kyudomaster/chu_giga/CAD/chu-tof.step

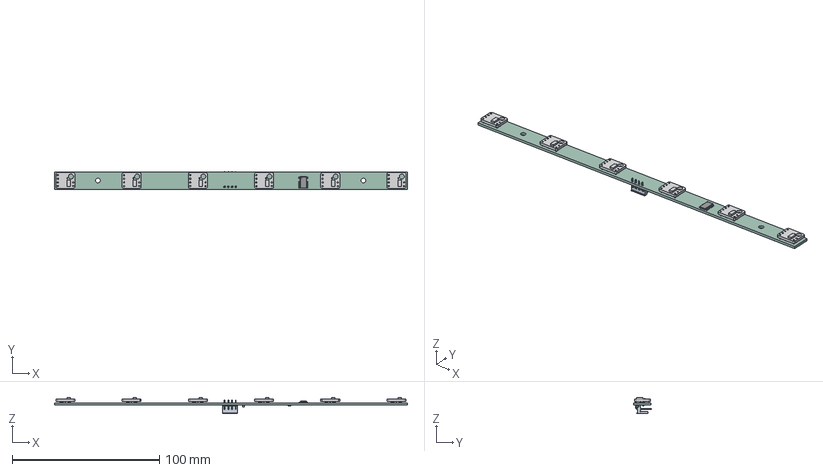
[picture p10: CAD file, 2026-06-13]
CAD/chu-tof.step
240.0 x 12.2 x 11.0 mm
GY530 ToF Sensor x 6
BODY-TSSOP
LEAD-TSSOP x 24
PIN1
C_0805_2012Metric
R_0805_2012Metric
chu_tof_PCB
